KGB-LABS/PROJETO_POS_GRADUACAO/controle_casa.kicad_sch

## KiCad design controle_casa.kicad_sch (2026-09-23)

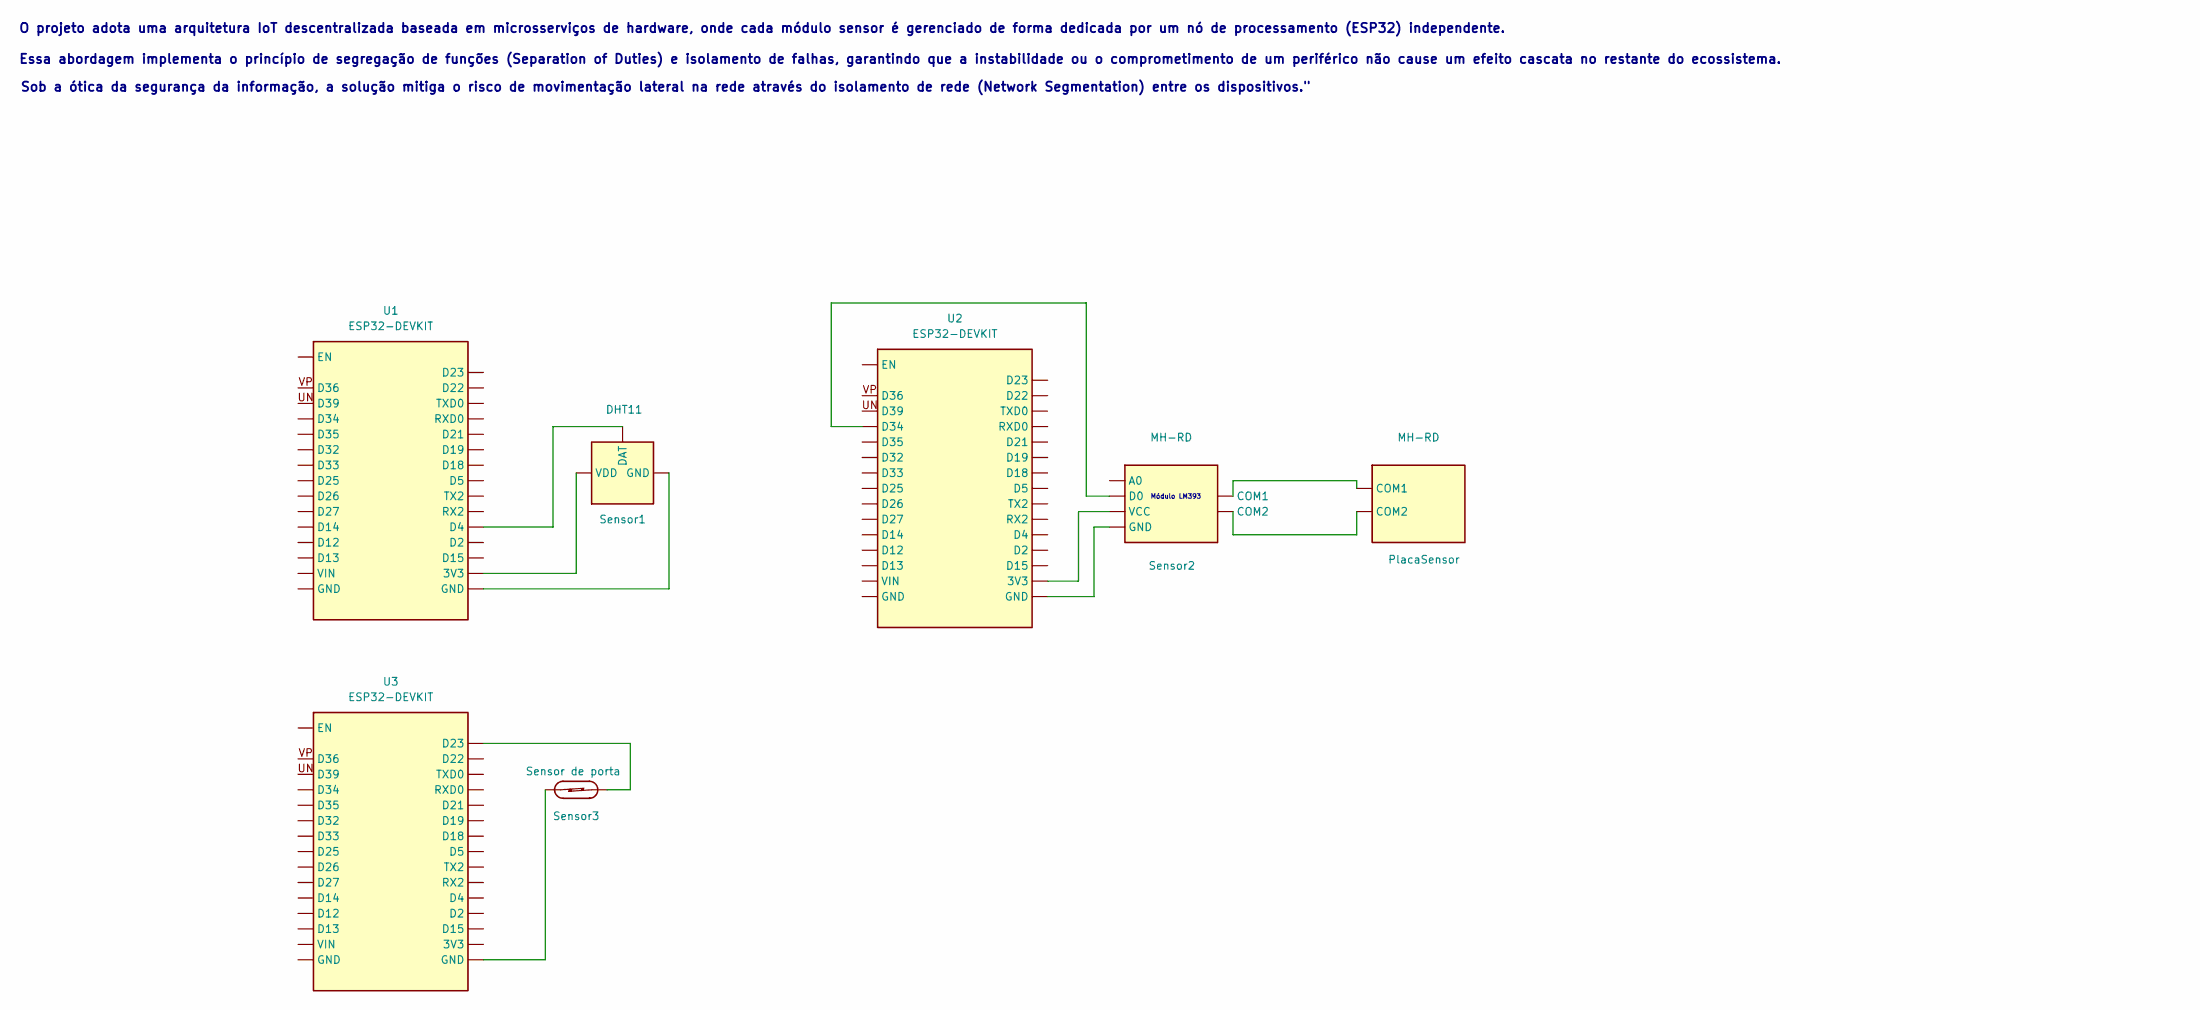
[picture p11: schematic controle_casa.kicad_sch]

Parts:
PlacaSensor: MH-RD; JEITA_SOIC-8_3.9x4.9mm_P1.27mm
Sensor1: DHT11; Aosong_DHT11_5.5x12.0_P2.54mm
Sensor2: MH-RD; JEITA_SOIC-8_3.9x4.9mm_P1.27mm
Sensor3: Sensor de porta
U1, U2, U3: ESP32-DEVKIT; ESP32-C6-MINI-1

Connections:
unnamed: Sensor1., U1. (D34)
unnamed: Sensor2., U2. (D34)
unnamed: Sensor3.1, U3. (D34)
unnamed: Sensor3.2, U3. (D34)

Notes on the sheet:
Sob a ótica da segurança da informação, a solução mitiga o risco de movimentação lateral na rede através do isolamento de rede (Network Segmentation) entre os dispositivos."
Essa abordagem implementa o princípio de segregação de funções (Separation of Duties) e isolamento de falhas, garantindo que a instabilidade ou o comprometimento de um periférico não cause um efeito cascata no restante do ecossistema.
Módulo LM393
O projeto adota uma arquitetura IoT descentralizada baseada em microsserviços de hardware, onde cada módulo sensor é gerenciado de forma dedicada por um nó de processamento (ESP32) independente.
